meeTeam05/smart-air/app/assets/images/device_placeholder.png

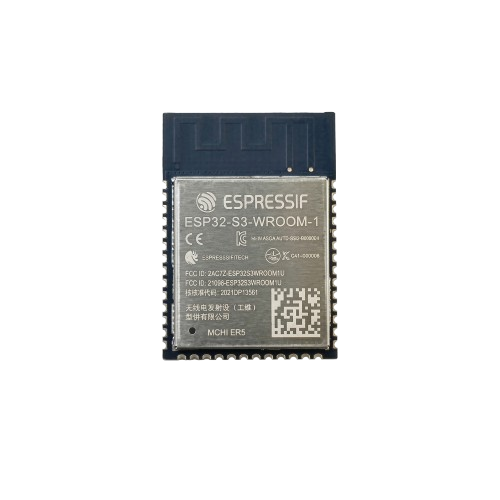
app/assets/images/device_placeholder.png
