meeTeam05/smart-air/app/test/goldens/goldens/atoms_step_dots_light.png

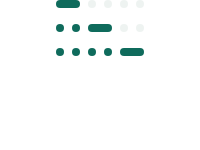
app/test/goldens/goldens/atoms_step_dots_light.png
