meeTeam05/smart-air/app/test/goldens/failures/screen_home_populated_light_testImage.png

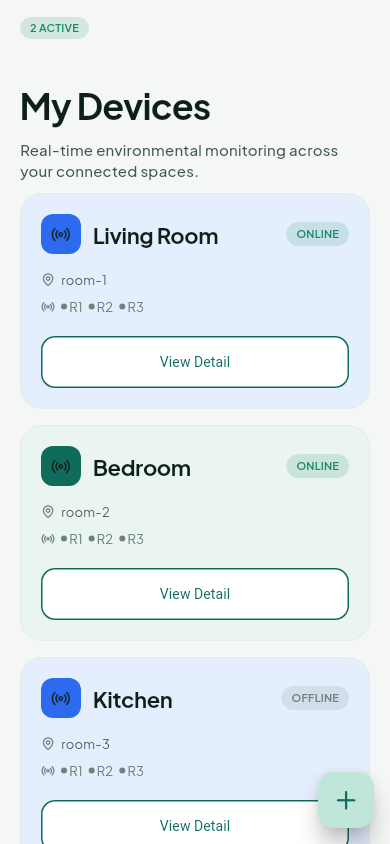
app/test/goldens/failures/screen_home_populated_light_testImage.png
