meeTeam05/smart-air/app/test/goldens/failures/screen_login_light_testImage.png

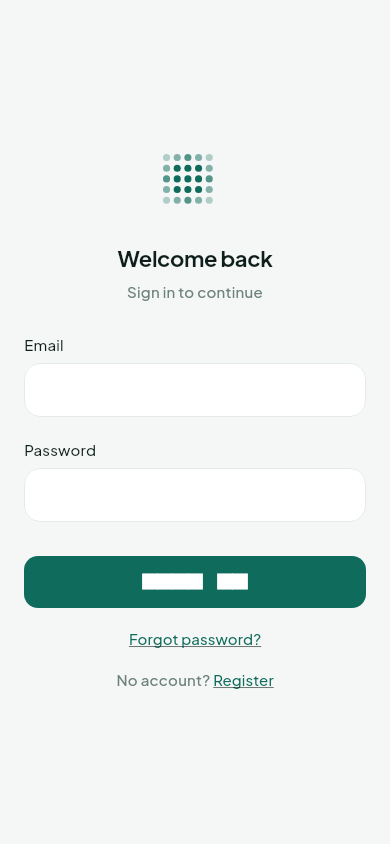
app/test/goldens/failures/screen_login_light_testImage.png
