meeTeam05/smart-air/app/test/goldens/goldens/atoms_buttons_dark.png

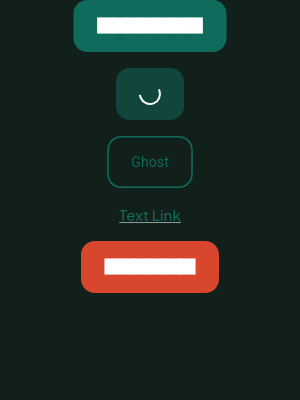
app/test/goldens/goldens/atoms_buttons_dark.png
