meeTeam05/smart-air/app/test/goldens/goldens/atoms_buttons_light.png

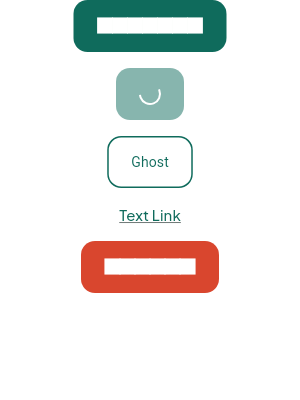
app/test/goldens/goldens/atoms_buttons_light.png
