meeTeam05/smart-air/app/test/goldens/goldens/atoms_empty_state_light.png

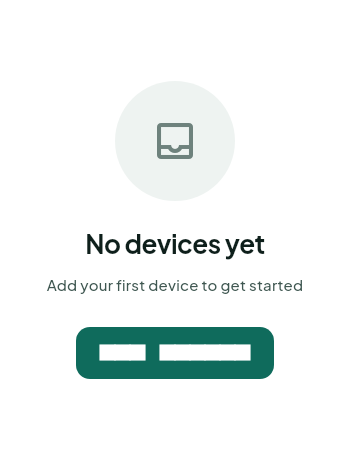
app/test/goldens/goldens/atoms_empty_state_light.png
