meeTeam05/smart-air/app/test/goldens/goldens/atoms_form_elements_light.png

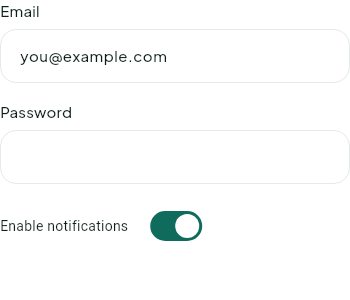
app/test/goldens/goldens/atoms_form_elements_light.png
