meeTeam05/smart-air/app/test/goldens/goldens/atoms_mode_card_light.png

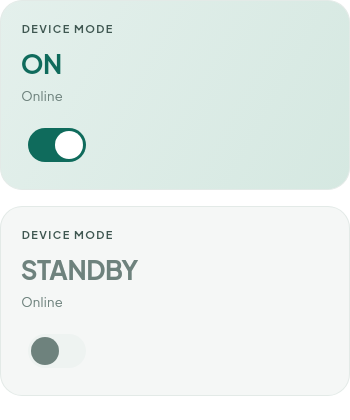
app/test/goldens/goldens/atoms_mode_card_light.png
