meeTeam05/smart-air/app/test/goldens/goldens/atoms_relay_cards_light.png

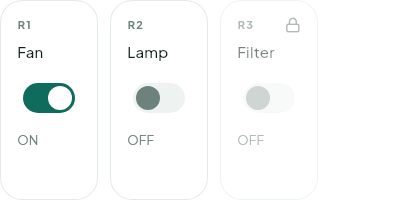
app/test/goldens/goldens/atoms_relay_cards_light.png
