meeTeam05/smart-air/app/test/goldens/goldens/atoms_sensor_tiles_light.png

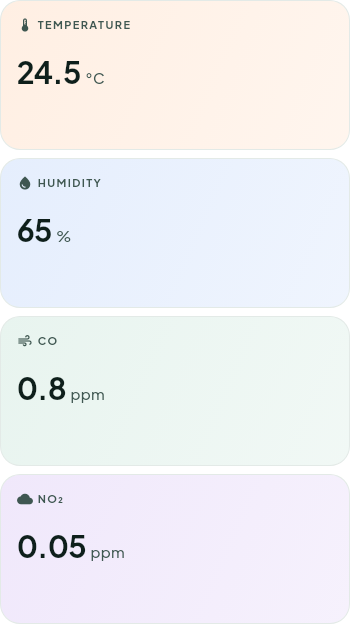
app/test/goldens/goldens/atoms_sensor_tiles_light.png
