meeTeam05/smart-air/app/test/goldens/goldens/screen_home_empty_light.png

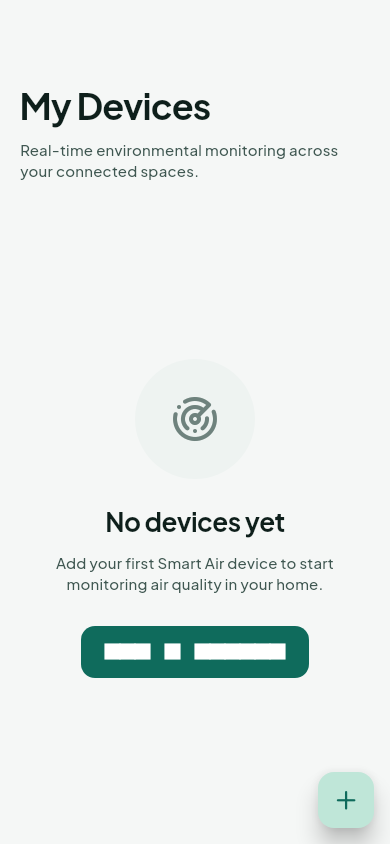
app/test/goldens/goldens/screen_home_empty_light.png
