meeTeam05/smart-air/app/test/goldens/goldens/screen_profile_light.png

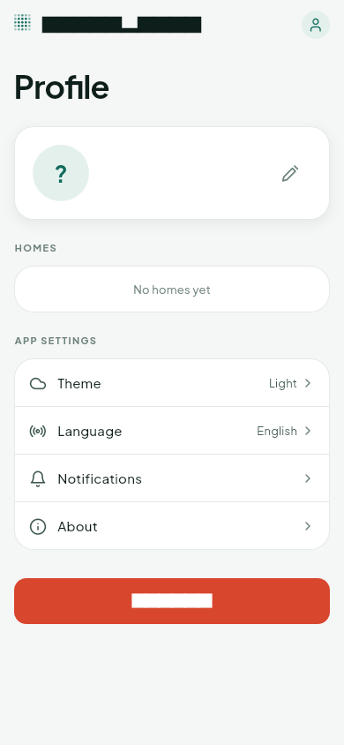
app/test/goldens/goldens/screen_profile_light.png
