meeTeam05/smart-air/app/test/goldens/failures/atoms_pills_light_isolatedDiff.png

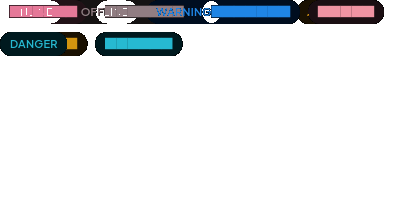
app/test/goldens/failures/atoms_pills_light_isolatedDiff.png
