meeTeam05/smart-air/app/test/goldens/failures/screen_login_dark_maskedDiff.png

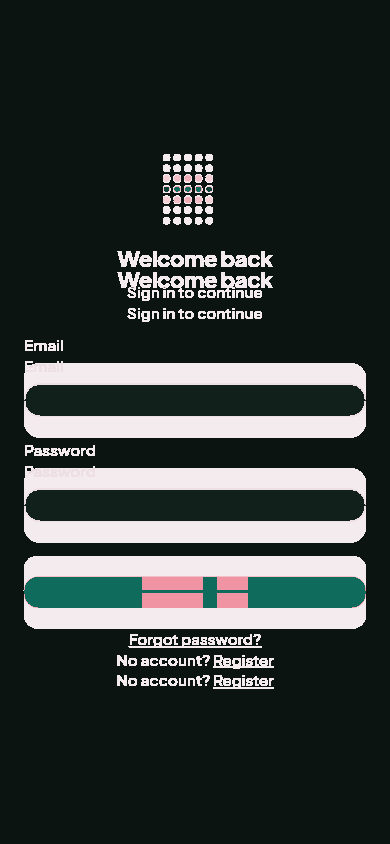
app/test/goldens/failures/screen_login_dark_maskedDiff.png
