meeTeam05/smart-air/app/test/goldens/goldens/atoms_history_row_light.png

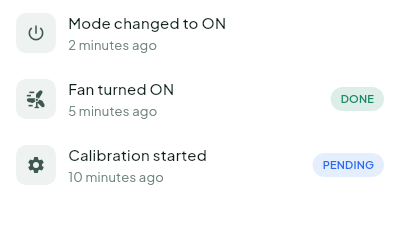
app/test/goldens/goldens/atoms_history_row_light.png
